ConfusedHello/USB-Mic/src/SPICE/DAC.asc

C1: cap; 0.000000022
C2: cap; 0.00047
R1: res; 16
R2: res; 3300
R3: res; 3300
R4: res; 32
V1: voltage; SINE(0 10 5); AC 10
Named nets: 0
.tran 2
.ac lin 1000 1 10000
