ConfusedHello/USB-Mic/src/SPICE/Mic.asc

C1: cap; 0.0000022
J1: njf; J113
R1: res; 1000000000; tol=5
R2: res; 250
R3: res; 1000000
R4: res; 1000000
R5: res; 2150
U1: OP07
V1: voltage; SINE(0 0.000115948 1000); AC 0.000115948; Cpar=0.000000000045
V2: voltage; 4.5
V3: voltage; 3.3
V4: voltage; 5
Named nets: 0
.tran 0.01
.ac lin 5000 1 1000
